Makerfabs/Lora-Soil-Moisture-Sensor/V3/example/Lora_Receiver_v1.0/Lora_Receiver_v1.0.ino

/*
   LoRaLib Receive Example

   This example listens for LoRa transmissions and tries to
   receive them. To successfully receive data, the following
   settings have to be the same on both transmitter
   and receiver:
    - carrier frequency
    - bandwidth
    - spreading factor
    - coding rate
    - sync word
    - preamble length

   For more detailed information, see the LoRaLib Wiki
   https://github.com/jgromes/LoRaLib/wiki

   For full API reference, see the GitHub Pages
   https://jgromes.github.io/LoRaLib/
*/

// include the library
#include <RadioLib.h>
#include <SPI.h>
#include "avr/boot.h"

// create instance of LoRa class using SX1278 module
// this pinout corresponds to RadioShield
// https://github.com/jgromes/RadioShield

#define DIO0 2
#define DIO1 6
//#define DIO2 7
//#define DIO5 8

#define LORA_RST 9
#define LORA_CS 10

#define SPI_MOSI 11
#define SPI_MISO 12
#define SPI_SCK 13


/*
Begin method:
Carrier frequency: 434.0 MHz (for SX1276/77/78/79 and RFM96/98) or 915.0 MHz (for SX1272/73 and RFM95/97)
Bandwidth: 125.0 kHz (dual-sideband)
Spreading factor: 9
Coding rate: 4/7
Sync word: SX127X_SYNC_WORD (0x12)
Output power: 10 dBm
Preamble length: 8 symbols
Gain: 0 (automatic gain control enabled)
Other:
Over-current protection: 60 mA
Inaccessible:
LoRa header mode: explicit
Frequency hopping: disabled

*/

#define FREQUENCY 915.0
#define BANDWIDTH 125.0
#define SPREADING_FACTOR 9
#define CODING_RATE 7
#define OUTPUT_POWER 10
#define PREAMBLE_LEN 8
#define GAIN 0

SX1276 radio = new Module(LORA_CS, DIO0, LORA_RST, DIO1);
//SX1278 radio = new Module(LORA_CS, DIO0, LORA_RST, DIO1, SPI, SPISettings());


void setup() {
  Serial.begin(115200);

  // initialize SX1278 with default settings
  Serial.print(F("Initializing ... "));

  //int state = radio.begin();
  int state = radio.begin(FREQUENCY, BANDWIDTH, SPREADING_FACTOR, CODING_RATE, SX127X_SYNC_WORD, OUTPUT_POWER, PREAMBLE_LEN, GAIN);
  if (state == ERR_NONE) {
    Serial.println(F("success!"));
  } else {
    Serial.print(F("failed, code "));
    Serial.println(state);
    while (true);
  }
  Serial.print(F("Waiting for incoming transmission ... "));
}

void loop() {
  //Serial.print(F("Waiting for incoming transmission ... "));

  // you can receive data as an Arduino String
  // NOTE: receive() is a blocking method!
  //       See example ReceiveInterrupt for details
  //       on non-blocking reception method.
  // NOTE: for spreading factor 6, the packet length
  //       must be known in advance, and provided to
  //       receive() method!
  String str;
  int state = radio.receive(str);

  // you can also receive data as byte array
  /*
    size_t len = 8;
    byte byteArr[len];
    int state = radio.receive(byteArr, len);
  */

  if (state == ERR_NONE) {
    // packet was successfully received
    Serial.println(F("success!"));

    // print data of the packet
    Serial.print(F("Data:\t\t\t"));
    Serial.println(str);

    // print RSSI (Received Signal Strength Indicator)
    // of the last received packet
    Serial.print(F("RSSI:\t\t\t"));
    Serial.print(radio.getRSSI());
    Serial.println(F(" dBm"));

    // print SNR (Signal-to-Noise Ratio)
    // of the last received packet
    Serial.print(F("SNR:\t\t\t"));
    Serial.print(radio.getSNR());
    Serial.println(F(" dB"));

    // print frequency error
    // of the last received packet
    Serial.print(F("Frequency error:\t"));
    Serial.print(radio.getFrequencyError());
    Serial.println(F(" Hz"));

  } else if (state == ERR_RX_TIMEOUT) {
    // timeout occurred while waiting for a packet
    //Serial.println(F("timeout!"));

  } else if (state == ERR_CRC_MISMATCH) {
    // packet was received, but is malformed
    Serial.println(F("CRC error!"));

  }

}
